yamamo2shun1/OTO_DEVICES/STM32CubeIDE/JUMBLEQ/Appli/Core/Inc/main.h

#define RESET_FROM_FW 1  // SigmaStudio+からのリセットを有効にする場合は0に設定
#define DSP_RESET_Pin GPIO_PIN_1
#define DSP_RESET_GPIO_Port GPIOH
#define S0_Pin GPIO_PIN_8
#define S0_GPIO_Port GPIOD
#define S1_Pin GPIO_PIN_9
#define S1_GPIO_Port GPIOD
#define S2_Pin GPIO_PIN_10
#define S2_GPIO_Port GPIOD
#define S3_Pin GPIO_PIN_12
#define S3_GPIO_Port GPIOB
#define CODEC_RESET_Pin GPIO_PIN_13
#define CODEC_RESET_GPIO_Port GPIOB
#define SW2_Pin GPIO_PIN_14
#define SW2_GPIO_Port GPIOD
#define SW1_Pin GPIO_PIN_15
#define SW1_GPIO_Port GPIOD
#define LED2_Pin GPIO_PIN_0
#define LED2_GPIO_Port GPIOD
#define LED1_Pin GPIO_PIN_1
#define LED1_GPIO_Port GPIOD
#define LED0_Pin GPIO_PIN_2
#define LED0_GPIO_Port GPIOD
#define UCPD_FLG_n_Pin GPIO_PIN_8
#define UCPD_FLG_n_GPIO_Port GPIOM
#define UCPD_FLG_n_EXTI_IRQn EXTI8_IRQn
#define UCPD_PWR_EN_Pin GPIO_PIN_9
#define UCPD_PWR_EN_GPIO_Port GPIOM
