yamamo2shun1/OTO_DEVICES/STM32CubeIDE/JUMBLEQ/Appli/Core/Inc/SigmaStudioFW.h

/*
 * File:			SigmaStudioFW.h
 *
 * Description:  	SigmaStudio System Framwork macro definitions. These
 *				macros should be implemented for your system's software.
 *
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
 * This software may only be used to program products purchased from
 * Analog Devices for incorporation by you into audio products that
 * are intended for resale to audio product end users. This software
 * may not be distributed whole or in any part to third parties.
 *
 * Copyright © 2024 Analog Devices, Inc. All rights reserved.
 */

#ifndef __SIGMASTUDIOFW_H__
#define __SIGMASTUDIOFW_H__

#include <stdint.h>

/*
 * TODO: Update for your system's data type
 */
typedef unsigned short ADI_DATA_U16;
typedef unsigned char ADI_REG_TYPE;

/*
 * Parameter data format
 */
#define SIGMASTUDIOTYPE_FIXPOINT 0
#define SIGMASTUDIOTYPE_INTEGER  1

#define DEVICE_ADDR_ADAU146XSCHEMATIC_1 0x00
// Larger DSP memory downloads are split into word-aligned blocks internally.
#define SIGMA_WRITE_BLOCK_MAX_PAYLOAD    4093U

/*
 * Write to a single Device register
 */
#define SIGMA_WRITE_REGISTER(devAddress, address, dataLength, data) \
    { /*TODO: implement macro or define as function*/               \
    }

/*
 * TODO: CUSTOM MACRO IMPLEMENTATION
 * Write to multiple Device registers
 */
// #define SIGMA_WRITE_REGISTER_BLOCK( devAddress, address, length, pData ) {/*TODO: implement macro or define as function*/}
void SIGMA_WRITE_REGISTER_BLOCK(uint8_t devAddress, uint16_t address, uint32_t length, uint8_t* pData);
void SIGMA_WRITE_REGISTER_BLOCK_IT(uint8_t devAddress, uint16_t address, uint16_t length, uint8_t* pData);

// Diagnostics for runtime DSP parameter write path (IT mode)
extern volatile uint32_t sigma_spi_it_write_calls;
extern volatile uint32_t sigma_spi_it_write_errors;
extern volatile uint32_t sigma_spi_it_write_timeouts;
extern volatile uint32_t sigma_spi_it_mutex_timeouts;

/*
 * Initialize SPI synchronization primitives for FreeRTOS
 * Must be called after FreeRTOS scheduler is started
 */
void SIGMA_SPI_Init(void);

void SIGMA_SAFELOAD_WRITE_DATA(uint8_t devAddress, uint16_t dataAddress, uint16_t length, uint8_t* pData);

/*
 * TODO: CUSTOM MACRO IMPLEMENTATION
 * Writes delay (in ms)
 */
// #define SIGMA_WRITE_DELAY(devAddress, length, pData) { /*TODO: implement macro or define as function*/ }
void SIGMA_WRITE_DELAY(uint8_t devAddress, uint16_t dataAddress, uint16_t length, uint8_t* pData);

/*
 * Read device registers
 */
// #define SIGMA_READ_REGISTER(devAddress, address, length, pData) { /*TODO: implement macro or define as function*/}
void SIGMA_READ_REGISTER(uint8_t devAddress, uint16_t address, uint16_t length, uint8_t* pData);
/*
 * Set a register field's value
 */
#define SIGMA_SET_REGSITER_FIELD(regVal, fieldVal, fieldMask, fieldShift) \
    {(regVal) = (((regVal) & (~(fieldMask))) | (((fieldVal) << (fieldShift)) && (fieldMask)))}

/*
 * Get the value of a register field
 */
#define SIGMA_GET_REGSITER_FIELD(regVal, fieldMask, fieldShift) \
    {((regVal) & (fieldMask)) >> (fieldShift)}

/*
 * Convert a floating-point value to SigmaDSP (5.23) fixed point format
 *    This optional macro is intended for systems having special implementation
 *    requirements (for example: limited memory size or endianness)
 */
#define SIGMASTUDIOTYPE_FIXPOINT_CONVERT(_value) \
    { /*TODO: IMPLEMENT MACRO*/                  \
    }

/*
 * Convert integer data to system compatible format
 *    This optional macro is intended for systems having special implementation
 *    requirements (for example: limited memory size or endianness)
 */
#define SIGMASTUDIOTYPE_INTEGER_CONVERT(_value) \
    { /*TODO: IMPLEMENT MACRO*/                 \
    }

#endif
