yamamo2shun1/OTO_DEVICES/STM32CubeIDE/JUMBLEQ/Appli/Core/Inc/ak4619.h

/*
 * ak4619.h
 *
 *  Created on: 2026/01/24
 *      Author: shuni
 */

#ifndef INC_AK4619_H_
#define INC_AK4619_H_

#include "main.h"

#define AK4619_MIC_GAIN_CH1   0U
#define AK4619_MIC_GAIN_CH2   1U
#define AK4619_MIC_GAIN_DB_0  0U
#define AK4619_MIC_GAIN_DB_27 27U

void AUDIO_Init_AK4619(uint32_t hz);

void AUDIO_Mic_Gain_AMP_Setting_Channel(uint8_t ch, uint8_t gain_db);

#endif /* INC_AK4619_H_ */
