yamamo2shun1/OTO_DEVICES/STM32CubeIDE/MX25UW25645GXDI00_STM32H7S3Z8T/Boot/Core/Src/main.c

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
/* Includes ------------------------------------------------------------------*/
#include "main.h"
#include "crc.h"
#include "extmem_manager.h"
#include "sbs.h"
#include "usb_otg.h"
#include "xspi.h"
#include "gpio.h"

/* USER CODE BEGIN Includes */
#include "boot_mode.h"
#include "led_status.h"
#include "uf2.h"
#include "uf2_msc.h"

/* USER CODE END Includes */

/* USER CODE BEGIN PD */
#define UF2_COMPLETE_SETTLE_MS 1500u
#define UF2_WRITE_IDLE_RESET_MS 3000u

/* USER CODE END PD */


void SystemClock_Config(void);
static void MPU_Config(void);
/* USER CODE BEGIN 0 */
static void boot_force_system_reset(void)
{
  HAL_GPIO_WritePin(LED0_GPIO_Port, LED0_Pin, GPIO_PIN_SET);
  HAL_GPIO_WritePin(LED1_GPIO_Port, LED1_Pin, GPIO_PIN_SET);
  HAL_GPIO_WritePin(LED2_GPIO_Port, LED2_Pin, GPIO_PIN_SET);

  for (volatile uint32_t i = 0u; i < 200000u; i++)
  {
    __NOP();
  }

  __disable_irq();
  __DSB();
  SCB->AIRCR = (0x5FAUL << SCB_AIRCR_VECTKEY_Pos) | SCB_AIRCR_SYSRESETREQ_Msk;
  __DSB();
  while (1)
  {
    __NOP();
  }
}

/* USER CODE END 0 */

/**
  * @brief  The application entry point.
  * @retval int
  */
int main(void)
{

  /* MPU Configuration--------------------------------------------------------*/
  MPU_Config();

  /* Enable the CPU Cache */

  /* Enable I-Cache---------------------------------------------------------*/
  SCB_EnableICache();

  /* Enable D-Cache---------------------------------------------------------*/
  SCB_EnableDCache();

  /* MCU Configuration--------------------------------------------------------*/

  /* Reset of all peripherals, Initializes the Flash interface and the Systick. */
  HAL_Init();

  /* Configure the system clock */
  SystemClock_Config();

  /* Initialize all configured peripherals */
  MX_GPIO_Init();
  MX_SBS_Init();
  MX_XSPI1_Init();
  MX_CRC_Init();
  MX_USB_OTG_HS_PCD_Init();
  MX_EXTMEM_MANAGER_Init();
  /* USER CODE BEGIN 2 */
  bool sw2_pressed = boot_mode_sw2_pressed();

  if (sw2_pressed)
  {
    led_status_set(LED_STATUS_UF2_IDLE);
    uf2_init();
    uf2_msc_init();
    uint32_t uf2_complete_since = 0u;
    uint32_t uf2_last_rx_tick = 0u;
    uint32_t uf2_last_rx_count = 0u;

    while (1)
    {
      uf2_msc_task();
      led_status_tick(HAL_GetTick());

      uint32_t now = HAL_GetTick();
      uint32_t rx_count = uf2_received_blocks();
      if (rx_count != uf2_last_rx_count)
      {
        uf2_last_rx_count = rx_count;
        uf2_last_rx_tick = now;
        uf2_complete_since = 0u;
      }

      bool uf2_write_idle = (rx_count > 0u) &&
                            (uf2_last_rx_tick != 0u) &&
                            ((now - uf2_last_rx_tick) >= UF2_WRITE_IDLE_RESET_MS);

      if (uf2_is_complete() || uf2_write_idle)
      {
        if (uf2_complete_since == 0u)
        {
          uf2_complete_since = now;
          led_status_set(LED_STATUS_VERIFY);
          HAL_GPIO_WritePin(LED0_GPIO_Port, LED0_Pin, GPIO_PIN_RESET);
          HAL_GPIO_WritePin(LED1_GPIO_Port, LED1_Pin, GPIO_PIN_SET);
          HAL_GPIO_WritePin(LED2_GPIO_Port, LED2_Pin, GPIO_PIN_SET);
        }

        if ((now - uf2_complete_since) < UF2_COMPLETE_SETTLE_MS)
        {
          continue;
        }

        boot_force_system_reset();
      }
      else
      {
        uf2_complete_since = 0u;
      }
    }
  }

  led_status_set(LED_STATUS_BOOT_JUMP);

  /* USER CODE END 2 */

  /* Launch the application */
  if (BOOT_OK != BOOT_Application())
  {
    Error_Handler();
  }
  /* Infinite loop */
  /* USER CODE BEGIN WHILE */
    while (1)
    {
    /* USER CODE END WHILE */

    /* USER CODE BEGIN 3 */
    }
  /* USER CODE END 3 */
}

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
 /* MPU Configuration */

static void MPU_Config(void)
{
  MPU_Region_InitTypeDef MPU_InitStruct = {0};

  /* Disables the MPU */
  HAL_MPU_Disable();

  /** Initializes and configures the Region and the memory to be protected
  */
  MPU_InitStruct.Enable = MPU_REGION_ENABLE;
  MPU_InitStruct.Number = MPU_REGION_NUMBER0;
  MPU_InitStruct.BaseAddress = 0x0;
  MPU_InitStruct.Size = MPU_REGION_SIZE_4GB;
  MPU_InitStruct.SubRegionDisable = 0x87;
  MPU_InitStruct.TypeExtField = MPU_TEX_LEVEL0;
  MPU_InitStruct.AccessPermission = MPU_REGION_NO_ACCESS;
  MPU_InitStruct.DisableExec = MPU_INSTRUCTION_ACCESS_DISABLE;
  MPU_InitStruct.IsShareable = MPU_ACCESS_NOT_SHAREABLE;
  MPU_InitStruct.IsCacheable = MPU_ACCESS_NOT_CACHEABLE;
  MPU_InitStruct.IsBufferable = MPU_ACCESS_NOT_BUFFERABLE;

  HAL_MPU_ConfigRegion(&MPU_InitStruct);

  /** Initializes and configures the Region and the memory to be protected
  */
  MPU_InitStruct.Number = MPU_REGION_NUMBER1;
  MPU_InitStruct.BaseAddress = 0x90000000;
  MPU_InitStruct.Size = MPU_REGION_SIZE_32MB;
  MPU_InitStruct.SubRegionDisable = 0x0;
  MPU_InitStruct.AccessPermission = MPU_REGION_FULL_ACCESS;
  MPU_InitStruct.DisableExec = MPU_INSTRUCTION_ACCESS_ENABLE;
  MPU_InitStruct.IsCacheable = MPU_ACCESS_CACHEABLE;
  MPU_InitStruct.IsBufferable = MPU_ACCESS_BUFFERABLE;

  HAL_MPU_ConfigRegion(&MPU_InitStruct);

  /** Initializes and configures the Region and the memory to be protected
  */
  MPU_InitStruct.Number = MPU_REGION_NUMBER2;
  MPU_InitStruct.BaseAddress = 0x24000000;
  MPU_InitStruct.Size = MPU_REGION_SIZE_256KB;
  MPU_InitStruct.DisableExec = MPU_INSTRUCTION_ACCESS_DISABLE;

  HAL_MPU_ConfigRegion(&MPU_InitStruct);

  /** Initializes and configures the Region and the memory to be protected
  */
  MPU_InitStruct.Number = MPU_REGION_NUMBER3;
  MPU_InitStruct.BaseAddress = 0x24040000;
  MPU_InitStruct.TypeExtField = MPU_TEX_LEVEL1;
  MPU_InitStruct.IsCacheable = MPU_ACCESS_NOT_CACHEABLE;
  MPU_InitStruct.IsBufferable = MPU_ACCESS_NOT_BUFFERABLE;

  HAL_MPU_ConfigRegion(&MPU_InitStruct);
  /* Enables the MPU */
  HAL_MPU_Enable(MPU_PRIVILEGED_DEFAULT);

}

/**
  * @brief  This function is executed in case of error occurrence.
  * @retval None
  */
void Error_Handler(void)
{
  /* USER CODE BEGIN Error_Handler_Debug */
    /* User can add his own implementation to report the HAL error return state */
    __disable_irq();
    while (1)
    {
    }
  /* USER CODE END Error_Handler_Debug */
}
#ifdef USE_FULL_ASSERT
/**
  * @brief  Reports the name of the source file and the source line number
  *         where the assert_param error has occurred.
  * @param  file: pointer to the source file name
  * @param  line: assert_param error line source number
  * @retval None
  */
void assert_failed(uint8_t *file, uint32_t line)
{
  /* USER CODE BEGIN 6 */
    /* User can add his own implementation to report the file name and line number,
       ex: printf("Wrong parameters value: file %s on line %d\r\n", file, line) */
  /* USER CODE END 6 */
}
#endif /* USE_FULL_ASSERT */
