yamamo2shun1/OTO_DEVICES/STM32CubeIDE/USB_HS_TEST/Appli/Core/Src/main.c

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
/* Includes ------------------------------------------------------------------*/
#include "main.h"
#include "adc.h"
#include "gpdma.h"
#include "i2c.h"
#include "sai.h"
#include "spi.h"
#include "ucpd.h"
#include "usbpd.h"
#include "usb_device.h"
#include "gpio.h"

/* USER CODE BEGIN Includes */
#include "SigmaStudioFW.h"
#include "oto_no_ita_dsp_ADAU146xSchematic_1.h"
#include "oto_no_ita_dsp_ADAU146xSchematic_1_Defines.h"
#include "oto_no_ita_dsp_ADAU146xSchematic_1_PARAM.h"
/* USER CODE END Includes */

/* USER CODE BEGIN PD */
// 32B境界ユーティリティ（既にあれば流用）
#define CACHE_ALIGN_UP(n)  (((n) + 31u) & ~31u)
#define CACHE_ALIGN_PTR(p) ((uint32_t*) (((uintptr_t) (p)) & ~31u))

/* USER CODE END PD */


/* USER CODE BEGIN PV */
extern USBD_HandleTypeDef hUsbDeviceHS;

extern DMA_NodeTypeDef Node_GPDMA1_Channel2;   // TXノード
extern DMA_QListTypeDef List_GPDMA1_Channel2;  // TXキュー

extern DMA_NodeTypeDef Node_GPDMA1_Channel3;
extern DMA_QListTypeDef List_GPDMA1_Channel3;

__attribute__((aligned(32))) uint32_t sai_buf[SAI_BUF_SIZE * 2];
__attribute__((section(".RAM_D1"), aligned(32))) uint32_t sai_tx_buf[SAI_BUF_SIZE * 2];

static inline void clean_ll_cache(void* p, size_t sz)
{
    uintptr_t a = (uintptr_t) p & ~31u;
    size_t n    = (sz + 31u) & ~31u;
    SCB_CleanDCache_by_Addr((uint32_t*) a, n);
}

volatile uint8_t g_rx_pending = 0;  // bit0: 前半, bit1: 後半 が溜まっている
volatile uint8_t g_tx_safe    = 1;  // 1: 前半に書いてOK, 2: 後半に書いてOK
volatile uint8_t g_tx_pending = 0;  // bit0: 前半空き, bit1: 後半空き（取りこぼし防止）

// === USER CODE END 0 ===

/* USER CODE END PV */

/* USER CODE BEGIN 0 */
int __io_putchar(uint8_t ch)
{
    return ITM_SendChar(ch);
}

void HAL_SAI_RxHalfCpltCallback(SAI_HandleTypeDef* hsai)
{
    if (hsai == &hsai_BlockA1)
    {
        g_rx_pending |= 0x01;
        __DMB();
    }
}

void HAL_SAI_RxCpltCallback(SAI_HandleTypeDef* hsai)
{
    if (hsai == &hsai_BlockA1)
    {
        g_rx_pending |= 0x02;
        __DMB();
    }
}

void HAL_SAI_TxHalfCpltCallback(SAI_HandleTypeDef* hsai)
{
    if (hsai == &hsai_BlockA2)
    {
        g_tx_safe = 1; /* 前半が“安全に書ける側”へ */
        g_tx_pending |= 0x01;
        __DMB();
        HalfTransfer_CallBack_HS();
    }
}

void HAL_SAI_TxCpltCallback(SAI_HandleTypeDef* hsai)
{
    if (hsai == &hsai_BlockA2)
    {
        g_tx_safe = 2; /* 後半が“安全に書ける側”へ */
        g_tx_pending |= 0x02;
        __DMB();
        TransferComplete_CallBack_HS();
    }
}

void HAL_SAI_ErrorCallback(SAI_HandleTypeDef* hsai)
{
    volatile uint32_t saiErr = hsai->ErrorCode;                                 // HAL_SAI_ERROR_*
    volatile uint32_t dmaErr = hsai->hdmarx ? hsai->hdmarx->ErrorCode : 0;      // HAL_DMA_ERROR_*
    volatile uint32_t csr    = hsai->hdmarx ? hsai->hdmarx->Instance->CSR : 0;  // DTEF/ULEF/USEF/TOF 等

    (void) saiErr;
    (void) dmaErr;
    (void) csr;  // ブレークして値を見る
}
/* USER CODE END 0 */

/**
 * @brief  The application entry point.
 * @retval int
 */
int main(void)
{
    /* Enable the CPU Cache */

    /* Enable I-Cache---------------------------------------------------------*/
    SCB_EnableICache();

    /* Enable D-Cache---------------------------------------------------------*/
    SCB_EnableDCache();

    /* MCU Configuration--------------------------------------------------------*/

    /* Update SystemCoreClock variable according to RCC registers values. */
    SystemCoreClockUpdate();

    /* Reset of all peripherals, Initializes the Flash interface and the Systick. */
    HAL_Init();

    /* Initialize all configured peripherals */
    MX_GPIO_Init();
    MX_GPDMA1_Init();
    MX_USB_DEVICE_Init();
    MX_UCPD1_Init();
    MX_I2C3_Init();
    MX_ADC2_Init();
    MX_ADC1_Init();
    MX_SPI5_Init();
    MX_SAI1_Init();
    MX_SAI2_Init();
    /* USER CODE BEGIN 2 */
    USB_EnableGlobalInt(USB_OTG_HS);
    USB_DevConnect(USB_OTG_HS);

    uint8_t sndData[1] = {0x00};

    HAL_GPIO_WritePin(LED0_GPIO_Port, LED0_Pin, 0);
    HAL_GPIO_WritePin(LED1_GPIO_Port, LED1_Pin, 0);
    HAL_GPIO_WritePin(LED2_GPIO_Port, LED2_Pin, 0);

    // Power Management
    // sndData[0] = 0x36;  // 00 11 0 11 0
    // HAL_I2C_Mem_Write(&hi2c3, (0b0010001 << 1), 0x00, I2C_MEMADD_SIZE_8BIT, sndData, sizeof(sndData), 10000);

    // Audio I/F format
    sndData[0] = 0xAC;  // 1 010 11 00 (TDM, 32bit, TDM128 I2S compatible, Falling, Slow)
    HAL_I2C_Mem_Write(&hi2c3, (0b0010001 << 1), 0x01, I2C_MEMADD_SIZE_8BIT, sndData, sizeof(sndData), 10000);

    // Reset Control
    sndData[0] = 0x10;  // 000 1 00 00
    HAL_I2C_Mem_Write(&hi2c3, (0b0010001 << 1), 0x02, I2C_MEMADD_SIZE_8BIT, sndData, sizeof(sndData), 10000);

    // System Clock Setting
    sndData[0] = 0x00;  // 00000 000(48kHz)
    // sndData[0] = 0x01;  // 00000 001(96kHz)
    HAL_I2C_Mem_Write(&hi2c3, (0b0010001 << 1), 0x03, I2C_MEMADD_SIZE_8BIT, sndData, sizeof(sndData), 10000);

    // ADC Input Setting
    sndData[0] = 0x55;  // 01 01 01 01
    HAL_I2C_Mem_Write(&hi2c3, (0b0010001 << 1), 0x0B, I2C_MEMADD_SIZE_8BIT, sndData, sizeof(sndData), 10000);

    // DAC Input Select Setting
    // sndData[0] = 0x0E;  // 00 00 11 10 (ADC1 -> DAC1, ADC2 -> DAC2)
    sndData[0] = 0x00;  // 00 00 00 00 (SDIN1 -> DAC1, SDIN2 -> DAC2)
    HAL_I2C_Mem_Write(&hi2c3, (0b0010001 << 1), 0x12, I2C_MEMADD_SIZE_8BIT, sndData, sizeof(sndData), 10000);

    // Power Management
    sndData[0] = 0x37;  // 00 11 0 11 1
    HAL_I2C_Mem_Write(&hi2c3, (0b0010001 << 1), 0x00, I2C_MEMADD_SIZE_8BIT, sndData, sizeof(sndData), 10000);
    // HAL_I2C_Mem_Read(&hi2c3, (0b0010001 << 1) | 1, 0x00, I2C_MEMADD_SIZE_8BIT, rcvData, sizeof(rcvData), 10000);

    HAL_Delay(100);
    default_download_ADAU146XSCHEMATIC_1();
    HAL_Delay(100);

    HAL_GPIO_WritePin(LED0_GPIO_Port, LED0_Pin, 1);
    HAL_GPIO_WritePin(LED1_GPIO_Port, LED1_Pin, 0);
    HAL_GPIO_WritePin(LED2_GPIO_Port, LED2_Pin, 0);

    // 1) LLI(ノード/キュー) を Clean（DMAが構造体を読む）
    SCB_CleanDCache_by_Addr(CACHE_ALIGN_PTR(&Node_GPDMA1_Channel2), CACHE_ALIGN_UP(sizeof(Node_GPDMA1_Channel2)));
    SCB_CleanDCache_by_Addr(CACHE_ALIGN_PTR(&List_GPDMA1_Channel2), CACHE_ALIGN_UP(sizeof(List_GPDMA1_Channel2)));

    // 2) 送信バッファを Clean（DMAが読むデータ本体）
    SCB_CleanDCache_by_Addr(CACHE_ALIGN_PTR(sai_tx_buf), CACHE_ALIGN_UP(sizeof(sai_tx_buf)));

    if (HAL_SAI_Transmit_DMA(&hsai_BlockA2, (uint8_t*) sai_tx_buf, SAI_BUF_SIZE * 2) != HAL_OK)
    {
        /* SAI transmit start error */
        Error_Handler();
    }

    HAL_Delay(1000);
    HAL_GPIO_WritePin(LED0_GPIO_Port, LED0_Pin, 1);
    HAL_GPIO_WritePin(LED1_GPIO_Port, LED1_Pin, 1);
    HAL_GPIO_WritePin(LED2_GPIO_Port, LED2_Pin, 0);

    clean_ll_cache(&Node_GPDMA1_Channel3, sizeof(Node_GPDMA1_Channel3));
    clean_ll_cache(&List_GPDMA1_Channel3, sizeof(List_GPDMA1_Channel3));

    if (HAL_SAI_Receive_DMA(&hsai_BlockA1, (uint8_t*) sai_buf, SAI_BUF_SIZE * 2) != HAL_OK)
    {
        /* SAI receive start error */
        Error_Handler();
    }

    HAL_GPIO_WritePin(LED0_GPIO_Port, LED0_Pin, 1);
    HAL_GPIO_WritePin(LED1_GPIO_Port, LED1_Pin, 1);
    HAL_GPIO_WritePin(LED2_GPIO_Port, LED2_Pin, 1);

    printf("hello.\n");
    printf("speed=%d (0:HS,1:FS)\n", hUsbDeviceHS.dev_speed);
    /* USER CODE END 2 */

    /* USBPD initialisation ---------------------------------*/
    MX_USBPD_Init();

    /* Infinite loop */
    /* USER CODE BEGIN WHILE */
    while (1)
    {
        /* USER CODE END WHILE */
        USBPD_DPM_Run();

        /* USER CODE BEGIN 3 */
    }
    /* USER CODE END 3 */
}

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
