yamamo2shun1/OTO_DEVICES/STM32CubeIDE/LED_BLINK_APP_JLINK/Appli/Core/Inc/SEGGER_RTT_Conf.h

/*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
---------------------------END-OF-HEADER------------------------------
File    : SEGGER_RTT_Conf.h
Purpose : Implementation of SEGGER real-time transfer (RTT) which
          allows real-time communication on targets which support
          debugger memory accesses while the CPU is running.
Revision: $Rev: 24316 $

*/

#ifndef SEGGER_RTT_CONF_H
#define SEGGER_RTT_CONF_H

#ifdef __IAR_SYSTEMS_ICC__
  #include <intrinsics.h>
#endif

/*********************************************************************
*
*       Defines, configurable
*
**********************************************************************
*/

//
// Take in and set to correct values for Cortex-A systems with CPU cache
//
//#define SEGGER_RTT_CPU_CACHE_LINE_SIZE            (32)          // Largest cache line size (in bytes) in the current system
//#define SEGGER_RTT_UNCACHED_OFF                   (0xFB000000)  // Address alias where RTT CB and buffers can be accessed uncached

//
// Most common case:
// Up-channel 0: RTT
// Up-channel 1: SystemView
//
#ifndef   SEGGER_RTT_MAX_NUM_UP_BUFFERS
  #define SEGGER_RTT_MAX_NUM_UP_BUFFERS             (3)     // Max. number of up-buffers (T->H) available on this target    (Default: 3)
#endif
//
// Most common case:
// Down-channel 0: RTT
// Down-channel 1: SystemView
//
#ifndef   SEGGER_RTT_MAX_NUM_DOWN_BUFFERS
  #define SEGGER_RTT_MAX_NUM_DOWN_BUFFERS           (3)     // Max. number of down-buffers (H->T) available on this target  (Default: 3)
#endif

#ifndef   BUFFER_SIZE_UP
  #define BUFFER_SIZE_UP                            (512)   // Fits with the RTT control block in the 1 KiB non-cacheable region
#endif

#ifndef   BUFFER_SIZE_DOWN
  #define BUFFER_SIZE_DOWN                          (16)    // Size of the buffer for terminal input to target from host (Usually keyboard input) (Default: 16)
#endif

#ifndef   SEGGER_RTT_PRINTF_BUFFER_SIZE
  #define SEGGER_RTT_PRINTF_BUFFER_SIZE             (64u)    // Size of buffer for RTT printf to bulk-send chars via RTT     (Default: 64)
#endif

#ifndef   SEGGER_RTT_MODE_DEFAULT
  #define SEGGER_RTT_MODE_DEFAULT                   SEGGER_RTT_MODE_NO_BLOCK_SKIP // Mode for pre-initialized terminal channel (buffer 0)
#endif

/*********************************************************************
*
*       RTT memcpy configuration
*
*       memcpy() is good for large amounts of data,
*       but the overhead is big for small amounts, which are usually stored via RTT.
*       With SEGGER_RTT_MEMCPY_USE_BYTELOOP a simple byte loop can be used instead.
*
*       SEGGER_RTT_MEMCPY() can be used to replace standard memcpy() in RTT functions.
*       This is may be required with memory access restrictions,
*       such as on Cortex-A devices with MMU.
*/
#ifndef   SEGGER_RTT_MEMCPY_USE_BYTELOOP
  #define SEGGER_RTT_MEMCPY_USE_BYTELOOP              0 // 0: Use memcpy/SEGGER_RTT_MEMCPY, 1: Use a simple byte-loop
#endif
//
// Example definition of SEGGER_RTT_MEMCPY to external memcpy with GCC toolchains and Cortex-A targets
//
//#if ((defined __SES_ARM) || (defined __CROSSWORKS_ARM) || (defined __GNUC__)) && (defined (__ARM_ARCH_7A__))
//  #define SEGGER_RTT_MEMCPY(pDest, pSrc, NumBytes)      SEGGER_memcpy((pDest), (pSrc), (NumBytes))
//#endif

//
// Target is not allowed to perform other RTT operations while string still has not been stored completely.
// Otherwise we would probably end up with a mixed string in the buffer.
// If using  RTT from within interrupts, multiple tasks or multi processors, define the SEGGER_RTT_LOCK() and SEGGER_RTT_UNLOCK() function here.
//
// SEGGER_RTT_MAX_INTERRUPT_PRIORITY can be used in the sample lock routines on Cortex-M3/4.
// Make sure to mask all interrupts which can send RTT data, i.e. generate SystemView events, or cause task switches.
// When high-priority interrupts must not be masked while sending RTT data, SEGGER_RTT_MAX_INTERRUPT_PRIORITY needs to be adjusted accordingly.
// (Higher priority = lower priority number)
// Default value for embOS: 128u
// Default configuration in FreeRTOS: configMAX_SYSCALL_INTERRUPT_PRIORITY: ( configLIBRARY_MAX_SYSCALL_INTERRUPT_PRIORITY << (8 - configPRIO_BITS) )
// In case of doubt mask all interrupts: 1 << (8 - BASEPRI_PRIO_BITS) i.e. 1 << 5 when 3 bits are implemented in NVIC
// or define SEGGER_RTT_LOCK() to completely disable interrupts.
//
#ifndef   SEGGER_RTT_MAX_INTERRUPT_PRIORITY
  #define SEGGER_RTT_MAX_INTERRUPT_PRIORITY         (0x20)   // Interrupt priority to lock on SEGGER_RTT_LOCK on Cortex-M3/4 (Default: 0x20)
#endif

/*********************************************************************
*
*       RTT lock configuration for SEGGER Embedded Studio,
*       Rowley CrossStudio and GCC
*/
#if ((defined(__SES_ARM) || defined(__SES_RISCV) || defined(__CROSSWORKS_ARM) || defined(__GNUC__) || defined(__clang__)) && !defined (__CC_ARM) && !defined(WIN32))
  #if (defined(__ARM_ARCH_6M__) || defined(__ARM_ARCH_8M_BASE__))
    #define SEGGER_RTT_LOCK()   {                                                                   \
                                    unsigned int _SEGGER_RTT__LockState;                                         \
                                  __asm volatile ("mrs   %0, primask  \n\t"                         \
                                                  "movs  r1, #1       \n\t"                         \
                                                  "msr   primask, r1  \n\t"                         \
                                                  : "=r" (_SEGGER_RTT__LockState)                                \
                                                  :                                                 \
                                                  : "r1", "cc"                                      \
                                                  );

    #define SEGGER_RTT_UNLOCK()   __asm volatile ("msr   primask, %0  \n\t"                         \
                                                  :                                                 \
                                                  : "r" (_SEGGER_RTT__LockState)                                 \
                                                  :                                                 \
                                                  );                                                \
                                }
  #elif (defined(__ARM_ARCH_7M__) || defined(__ARM_ARCH_7EM__) || defined(__ARM_ARCH_8M_MAIN__) || defined(__ARM_ARCH_8_1M_MAIN__))
    #ifndef   SEGGER_RTT_MAX_INTERRUPT_PRIORITY
      #define SEGGER_RTT_MAX_INTERRUPT_PRIORITY   (0x20)
    #endif
    #define SEGGER_RTT_LOCK()   {                                                                   \
                                    unsigned int _SEGGER_RTT__LockState;                                         \
                                  __asm volatile ("mrs   %0, basepri  \n\t"                         \
                                                  "mov   r1, %1       \n\t"                         \
                                                  "msr   basepri, r1  \n\t"                         \
                                                  : "=r" (_SEGGER_RTT__LockState)                                \
                                                  : "i"(SEGGER_RTT_MAX_INTERRUPT_PRIORITY)          \
                                                  : "r1", "cc"                                      \
                                                  );
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
